TMO2018/C64-ROM-Adapter-Longboard/C64-Prog-Adapter-LB/Rev1_0/pic/C64-Prog-Adapter - 4.jpg

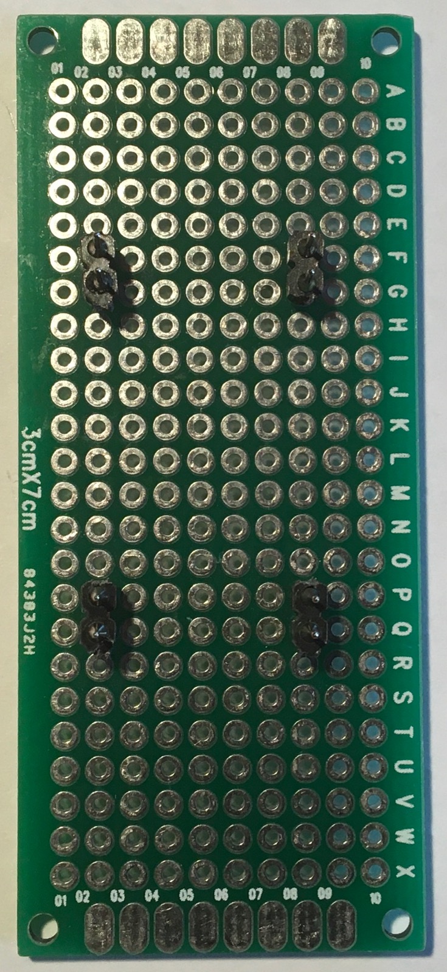
C64-Prog-Adapter-LB/Rev1_0/pic/C64-Prog-Adapter - 4.jpg
